k3ldar/PowerControlHub/KiCad/SmartFuseBox_PCB_Design_Specification.docx

# SmartFuseBox PCB Design Specification

# 1. Project Overview

The SmartFuseBox is a prototype PCB designed for both marine and home automation environments. It is based on the ESP32-S3 DevKitC-1 (N16R8) development board, which is mounted using headers to allow easy replacement. The board distributes 12V power through 8 relay channels (up to 5A each), includes at least 6 sensor input ports, a CAN bus interface, and monitoring features such as an onboard temperature sensor, buzzer, and fan connector. The system is designed for robust operation in demanding environments.

# 2. KiCad Project Structure

The KiCad project is structured as follows:

SmartFuseBox-PCB/
├── SmartFuseBox.kicad_pro
├── SmartFuseBox.kicad_sch ← root sheet (hierarchy only)
├── sheets/
│ ├── Power.kicad_sch
│ ├── ESP32_Module.kicad_sch
│ ├── Relays.kicad_sch
│ ├── Sensors.kicad_sch
│ └── Comms_Monitoring.kicad_sch
├── SmartFuseBox.kicad_pcb
└── gerbers/

# 3. ESP32-S3 DevKitC-1 Integration

The ESP32-S3 DevKitC-1 is mounted via dual-row headers. Essential pins for relays, sensors, CAN, buzzer, and fan are routed appropriately. USB access is maintained for programming. The ESP32 requires 3.3V power and robust grounding with short return paths.

# 4. Power System

The board accepts 12V DC input (up to 40A), distributed across 8 relays. DC-DC converters step down to 5V and 3.3V. Input filtering, reverse polarity protection, and fusing are required. Power planes are used for 12V, 5V, and 3.3V.

# 5. Relay Output System

8 relays with 12V coils (5A each) are driven by MOSFETs or transistors. Flyback diodes suppress voltage spikes. Relay outputs are connected to screw terminals. High-current traces use thick copper and are isolated from logic.

# 6. Sensor & IO Ports

At least 6 sensor ports provide 5V, 3.3V, GND, and two signal pins. All inputs include ESD protection and filtering. Screw terminals are recommended. Ports using GPIO35/36 support analog sensors. GPIO47/48 are digital-only. I2C-capable pairs include GPIO8/9 and GPIO10/11.

# 7. Communication Interfaces

A CAN transceiver interfaces with GPIO38 (TX) and GPIO39 (RX). Proper grounding and shielding are required. Termination resistors should be included as needed.

# 8. Monitoring & Auxiliary Features

Includes onboard temperature sensor (GPIO3), buzzer (GPIO1), and fan control (GPIO2). Optional status LEDs may be added.

# 9. Connector Strategy

Screw terminals are used for all power and sensor connections. ESP32 is socketed via headers. Dedicated connectors are provided for CAN, fan, and buzzer.

# 10. 4-Layer PCB Stackup Specification

Layer 1 — Top Layer: Signal + Low-Current Routing
Layer 2 — Inner Layer 1: Solid Ground Plane
Layer 3 — Inner Layer 2: Power Plane (12V, 5V, 3.3V)
Layer 4 — Bottom Layer: High-Current Relay Routing

# 11. Recommended Terminal Blocks

Use 5.0 mm pitch screw terminal blocks (≥10A rated) for power and relay outputs. Recommended series include:
- Phoenix Contact MKDS 5.08
- Wurth WR-TB series
- KF350-5.0 (generic)
Sensor ports may use 3.5 mm pitch blocks. All terminals should support AWG 12–24 wire sizes.

# Sheets

## Sheet 1 – Power Management

Circuit

Ref | Part | Value | KiCad Symbol | KiCad Footprint
J1 | Screw terminal 2-pin | 12V IN | Connector_PinHeader_2.54mm:PinHeader_1x02 | TerminalBlock_Phoenix:TerminalBlock_Phoenix_MPT-2.54mm_2P
F1 | Mini blade fuse holder | 20A | Device:Fuse | Fuse:Fuse_BelFuse_0AFF
Q1 | IRF9540N | P-ch MOSFET | Device:Q_PMOS_GSD | Package_TO_SOT_THT:TO-220-3_Vertical
TVS1 | P6KE15A | TVS 15V | Device:D_TVS | Diode_THT:D_DO-204AC
C1 | Electrolytic | 470µF/25V | Device:C | Capacitor_THT:CP_Radial_D10.0mm_P5.00mm
U1 | LM2596T-5.0 | Buck regulator | Regulator_Switching:LM2596T-5 | Package_TO_SOT_THT:TO-263-5_Vertical
L1 | Power inductor | 100µH/3A | Device:L | Inductor_THT:L_Radial_D8.0mm_P5.00mm
D1 | 1N5822 | Schottky 3A | Device:D_Schottky | Diode_THT:D_DO-201AD
C2 | Electrolytic | 100µF/10V | Device:C | Capacitor_THT:CP_Radial_D6.3mm_P2.50mm
U2 | AMS1117-3.3 | LDO 3.3V | Regulator_Linear:AMS1117-3.3 | Package_TO_SOT_SMD:SOT-223-3_TabPin2
C4/C5 | Tantalum | 10µF/10V | Device:C | Capacitor_SMD:C_0805_2012Metric

## Sheet 2 – ESP32-S3 Module

Houses the ESP32-S3 DevKitC-1 (N16R8) via two 20-pin female headers. All GPIO signals fan out as named nets to other sheets.

Please see 12. ESP32-S3 Pin Mapping

## Sheet 3 – Relay Drivers and Outputs

8-channel relay control using the ULN2803A Darlington array. Each relay has a status LED and a 3-pin screw terminal output (COM, NO, NC).

Ref | Part | Value | KiCad Symbol | KiCad Footprint
U3 | ULN2803ADWR | 8-ch Darlington | Driver_FET:ULN2803A | Package_SO:SOIC-18W_7.5x11.6mm_P1.27mm
RL1–RL8 | HRS4H-S-DC12V | 12V coil 10A SPDT | Relay_Electromechanical:G5LE-1 | Relay_THT:Relay_SPDT_HRS4H
J_RL1–8 | Screw terminal 3-pin | Relay output | Connector:Screw_Terminal_01x03 | TerminalBlock_Phoenix:TerminalBlock_Phoenix_MPT-2.54mm_3P
R_NET1 | Resistor network | 1kΩ×8 | Device:R_Network08 | Resistor_SMD:R_Array_Convex_8x0402
LED1–8 | LED 3mm green | — | Device:LED | LED_THT:LED_D3.0mm
R_LED1–8 | Resistor | 470Ω 0402 | Device:R | Resistor_SMD:R_0402
C_RL | Electrolytic | 100µF/25V | Device:C | Capacitor_THT:CP_Radial_D8.0mm_P5.00mm

## Sheet 4 - Sensor Ports and Switch Inputs

Six 5-pin sensor connectors (5V, 3.3V, GND, SIG1, SIG2) and four 2-pin switch/water-sensor inputs.

SENSOR_PORT_n (5-pin screw terminal):

Pin 1: +5V (from power rail, 100mA polyfuse per port: PTC_n)

Pin 2: +3.3V (from power rail, 100mA polyfuse per port)

Pin 3: GND

Pin 4: SIG1 → R_PU (10kΩ pullup to 3.3V) → ESP32 GPIO

Pin 5: SIG2 → R_PU (10kΩ pullup to 3.3V) → ESP32 GPIO

ESD protection:

D_ESD: PRTR5V0U2X or similar dual-channel TVS on SIG1/SIG2

# 12. ESP32-S3 Pin Mapping

## Relay Control Outputs

Relay Channel | ESP32 GPIO | Capabilities | Notes
Relay 1 | GPIO4 | Digital
Relay 2 | GPIO5 | Digital
Relay 3 | GPIO6 | Digital
Relay 4 | GPIO7 | Digital
Relay 5 | GPIO15 | Digital
Relay 6 | GPIO16 | Digital
Relay 7 | GPIO17 | Digital
Relay 8 | GPIO18 | Digital

## Sensor Input Ports

Sensor Port | Signal A | Signal B | Capabilities | Notes
Sensor 1 | GPIO8 | GPIO9 | Digital / I2C | I2C SDA/SCL capable
Sensor 2 | GPIO10 | GPIO11 | Digital / I2C | I2C SDA/SCL capable
Sensor 3 | GPIO12 | GPIO13 | Digital
Sensor 4 | GPIO14 | GPIO21 | Digital
Sensor 5 | GPIO47 | GPIO48 | Digital only | No ADC support
Sensor 6 | GPIO35 | GPIO36 | Analog only | ADC input only

## CAN Bus Interface

Function | ESP32 GPIO | Capabilities | Notes
CAN TX | GPIO38 | Digital
CAN RX | GPIO39 | Digital

## UART Interface

Function | ESP32 GPIO | Capabilities | Notes
UART TX | GPIO43 | USB-CDC | Avoid if using native USB
UART RX | GPIO44 | USB-CDC | Avoid if using native USB

⚠ If USB-CDC is used, reassign UART to GPIO1/2 or GPIO17/18.

## Auxiliary Outputs

Function | ESP32 GPIO | Capabilities | Notes
Buzzer | GPIO1 | Digital | Can be used for UART TX if needed
Cooling Fan | GPIO2 | Digital | Can be used for UART RX if needed

## Board Monitoring

Function | ESP32 GPIO | Capabilities | Notes
Temperature Sensor | GPIO3 | Analog | ADC input

## Reserved / Spare GPIO

GPIO | Capabilities | Notes
GPIO40 | Digital
GPIO41 | Digital
GPIO42 | Digital
GPIO45 | Input only | Do not use for output
GPIO46 | Input only | Do not use for output

## Power Pins

Function | Connection
5V | 5V regulator output
3.3V | 3.3V regulator output
GND | Ground plane
