k3ldar/PowerControlHub/KiCad/SmartFuseBox_PCB_Design_Specification.odt

SmartFuseBox PCB Design Specification

# 1. Project Overview

The SmartFuseBox is a prototype PCB designed for both marine and home automation environments. It is based on the ESP32-S3 DevKitC-1 (N16R8) development board, which is mounted using headers to allow easy replacement. The board is responsible for distributing 12V power through 8 relay channels, each capable of handling up to 5A. It includes multiple sensor input ports (minimum of 6), a CAN bus interface for future expansion, and monitoring features such as an onboard temperature sensor, buzzer, and fan connector. The system is designed for robust operation in demanding environments, ensuring reliable power distribution and sensor integration.

# 2. KiCad Project Structure

The KiCad project is structured as follows:

SmartFuseBox-PCB/
├── SmartFuseBox.kicad_pro
├── SmartFuseBox.kicad_sch ← root sheet (hierarchy only)
├── sheets/
│ ├── Power.kicad_sch
│ ├── ESP32_Module.kicad_sch
│ ├── Relays.kicad_sch
│ ├── Sensors.kicad_sch
│ └── Comms_Monitoring.kicad_sch
├── SmartFuseBox.kicad_pcb
└── gerbers/

• Power.kicad_sch: Defines the power input, regulation, and distribution circuits.
• ESP32_Module.kicad_sch: Contains the ESP32-S3 DevKitC-1 module and its connections.
• Relays.kicad_sch: Details the relay driver circuits and output connections.
• Sensors.kicad_sch: Defines the sensor input ports and signal conditioning.
• Comms_Monitoring.kicad_sch: Contains the CAN transceiver, temperature sensor, buzzer, and fan control circuits.

# 3. ESP32-S3 DevKitC-1 Integration

The ESP32-S3 DevKitC-1 is mounted via dual-row headers to allow easy replacement. Essential pins for controlling relays, reading sensor inputs, and interfacing with the CAN bus, buzzer, and fan must be routed to the appropriate circuits. USB access should be maintained for programming and debugging. The ESP32 requires 3.3V power and proper decoupling. Grounding must be robust, with short return paths and minimal noise coupling from high-current circuits.

# 4. Power System

The board accepts a 12V DC input capable of supplying up to 40A, distributed across 8 relay outputs. DC-DC converters step down the voltage to 5V and 3.3V for logic and sensors. Input filtering, reverse polarity protection, and fusing are required. Power planes should be used for 12V, 5V, and 3.3V, with careful placement of regulators to minimize noise and voltage drops. Recommended regulators include buck converters with sufficient current capacity and thermal management.

# 5. Relay Output System

The board includes 8 relays with 12V coils, each capable of switching up to 5A. Flyback diodes must be placed across each relay coil to suppress voltage spikes. MOSFET or transistor drivers are used to interface the ESP32 with the relays. Relay outputs are connected to screw terminals for easy wiring. High-current traces should be wide and use thick copper (e.g., 2 oz) to handle the load. Logic and high-current paths must be isolated to prevent interference.

# 6. Sensor & IO Ports

The board provides at least 6 sensor ports, each offering 5V, 3.3V, GND, and two signal pins. Additional digital inputs are available for switches or water sensors. All sensor inputs should include ESD protection and filtering. Screw terminals are recommended for sensor connections, with clear labeling and spacing for ease of use.

# 7. Communication Interfaces

A CAN transceiver is included for communication with future expansion boards. The CAN interface should use a standard connector and include termination resistors as needed. ESP32 GPIOs must be mapped appropriately to the CAN transceiver. Proper grounding and shielding practices should be followed to ensure signal integrity.

# 8. Monitoring & Auxiliary Features

The board includes an onboard temperature sensor for thermal monitoring, a buzzer for audible alerts, and a fan connector for active cooling. Optional status LEDs may be added for visual feedback. These components should be placed to avoid interference with other circuits and to ensure effective operation.

# 9. Connector Strategy

Screw terminals are used for all power and sensor connections to simplify wiring. The ESP32 is connected via header pins to allow easy replacement. Dedicated connectors are provided for the CAN interface, fan, and buzzer. All connectors should be clearly labeled and positioned for accessibility.

# 10. 4-Layer PCB Stackup Specification

## Layer 1 — Top Layer (Signal + Low-Current Routing)

This layer handles ESP32 high-speed signals, sensor IO, CAN bus, and control lines to relay drivers. It includes local decoupling capacitors and sensitive analog traces. Keep-out zones are defined around high-current relay pads. Critical signals such as the ESP32 crystal, USB, and boot pins are routed with minimal length.

## Layer 2 — Inner Layer 1 (Solid Ground Plane)

A continuous ground plane provides a low-impedance return path for high-speed signals and shields logic from high-current layers. Stitching vias are placed around the board perimeter. All components including the CAN transceiver, ESP32, sensors, and relay drivers are grounded to this layer.

## Layer 3 — Inner Layer 2 (Power Plane)

This layer distributes 12V, 5V, and 3.3V power. Wide copper pours are used for high-current 12V paths. Thermal reliefs are applied to connector pads. Logic and relay power are separated to reduce noise. Decoupling capacitors connect to this layer through vias.

## Layer 4 — Bottom Layer (High-Current Relay Routing)

This layer routes high-current relay outputs and coil connections. Heavy copper pours are used for 12V switching. Screw terminal connections are routed here. Logic traces are physically separated from high-current paths. Fan and buzzer power lines are also routed on this layer.

# 11. Summary

The SmartFuseBox PCB is a robust, modular power distribution and sensor interface board based on the ESP32-S3 DevKitC-1. It supports 12V power switching, sensor integration, and communication via CAN bus. The 4-layer PCB design ensures reliable operation by separating signal, ground, power, and high-current paths. This specification provides a comprehensive guide for implementing the design in KiCad.

# ESP32-S3 Pin Allocation

# ESP32-S3 DevKRelay Control Outputs (8 Channels)

These GPIO pins drive the relay driver circuits (via MOSFET/transistor drivers):

Relay Channel | ESP32 GPIO
Relay 1 | GPIO4
Relay 2 | GPIO5
Relay 3 | GPIO6
Relay 4 | GPIO7
Relay 5 | GPIO15
Relay 6 | GPIO16
Relay 7 | GPIO17
Relay 8 | GPIO18

### Sensor Input Ports

Each sensor connector provides:

- 5V
- 3.3V
- GND
- Signal A
- Signal B

Recommended GPIO assignments:

Sensor Port | Signal A | Signal B
Sensor 1 | GPIO8 | GPIO9
Sensor 2 | GPIO10 | GPIO11
Sensor 3 | GPIO12 | GPIO13
Sensor 4 | GPIO14 | GPIO21
Sensor 5 | GPIO47 | GPIO48
Sensor 6 | GPIO35 | GPIO36

These pins support:

- Digital sensors
- Analog sensors
- I2C devices
- Simple switch inputs

### CAN Bus Interface

The CAN bus is implemented using an external CAN transceiver.

Function | ESP32 GPIO
CAN TX | GPIO38
CAN RX | GPIO39

### UART Interface (External Devices / Debug)

Function | ESP32 GPIO
UART TX | GPIO43
UART RX | GPIO44

### Auxiliary Outputs

Function | ESP32 GPIO
Buzzer | GPIO1
Cooling Fan Control | GPIO2

### Board Monitoring

Function | ESP32 GPIO
On-board Temperature Sensor | GPIO3 (Analog Input)

### Reserved / Spare GPIO

The following pins should remain available for future expansion and should be routed to 5.0mm pitch PCB screw terminal blocks:

- GPIO40
- GPIO41
- GPIO42
- GPIO45
- GPIO46

### Power Pins

The following ESP32 power pins must be connected appropriately:

Function | Connection
5V | 5V regulator output
3.3V | 3.3V regulator output
GND | Ground plane

# itC-1 N16R8 ESP32 S3 WROOM-1-N16R8
