k3ldar/PowerControlHub/NextionControlPanel/src/Markers/CardinalMarkers.png

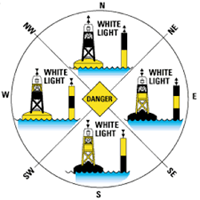
NextionControlPanel/src/Markers/CardinalMarkers.png
