k3ldar/PowerControlHub/NextionControlPanel/src/Markers/IsolatedDanger.png

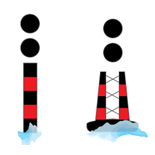
NextionControlPanel/src/Markers/IsolatedDanger.png
