k3ldar/PowerControlHub/NextionControlPanel/src/Markers/LateralPort.png

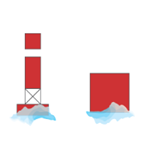
NextionControlPanel/src/Markers/LateralPort.png
