k3ldar/PowerControlHub/NextionControlPanel/src/Markers/PreferredChannelPort.png

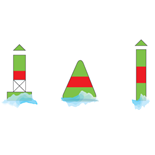
NextionControlPanel/src/Markers/PreferredChannelPort.png
