k3ldar/PowerControlHub/NextionControlPanel/src/Markers/SafeWater.png

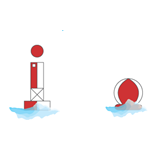
NextionControlPanel/src/Markers/SafeWater.png
