k3ldar/PowerControlHub/NextionControlPanel/src/Moon Phases/Phases.jpg

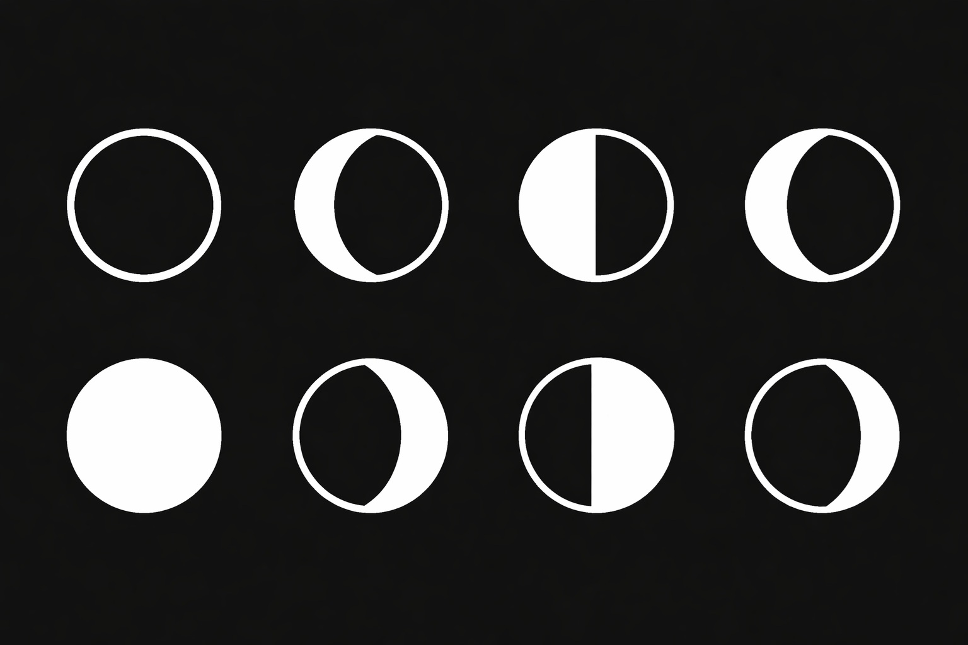
NextionControlPanel/src/Moon Phases/Phases.jpg
