k3ldar/PowerControlHub/PowerControlHub/SensorFactory.h

/*
 * PowerControlHub
 * Copyright (C) 2025 Simon Carter (s1cart3r@gmail.com)
 *
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
 * You should have received a copy of the GNU General Public License
 * along with this program. If not, see <https://www.gnu.org/licenses/>.
 */
#pragma once

#include "Local.h"
#include "Config.h"
#include "BaseSensor.h"
#include "MessageBus.h"
#include "SensorCommandHandler.h"
#include "WarningManager.h"
#include "RelayController.h"
#include "IWifiController.h"
#include "IBluetoothRadio.h"

#if defined(SD_CARD_SUPPORT)
#include "SdCardLogger.h"
#endif

#include "WaterSensorHandler.h"
#include "Dht11SensorHandler.h"
#include "GpsSensorHandler.h"
#include "LightSensorHandler.h"
#include "SystemSensorHandler.h"
#include "BinaryPresenceSensor.h"
#include "VoltageSensorHandler.h"
#include "ReedSensorHandler.h"

/**
 * @brief Dependencies injected by PowerControlHubApp into SensorFactory::create().
 *
 * Grouping them into a struct keeps the create() signature manageable and means
 * adding a new shared dependency does not require touching every call-site.
 */
struct SensorFactoryContext
{
    MessageBus* messageBus;
    BroadcastManager* broadcastManager;
    SensorCommandHandler* sensorCommandHandler;
    WarningManager* warningManager;
    RelayController* relayController;
    IWifiController* wifiController;
    IBluetoothRadio* bluetoothRadio;
    Stream* gpsSerial;

#if defined(SD_CARD_SUPPORT)
    SdCardLogger*         sdCardLogger;
#endif
};

/**
 * @brief Boot-time factory that converts SensorsConfig entries into live BaseSensor instances.
 *
 * Called once during setup(), after ConfigManager::load() has populated SensorsConfig.
 * All allocations are permanent for the lifetime of the device — no sensor is ever
 * destroyed or recreated at runtime.  A reboot is required for config changes to
 * take effect, which is intentional.
 *
 * Usage (inside PowerControlHubApp::setup):
 * @code
 *   SensorFactoryContext ctx{ &_messageBus, ... };
 *   uint8_t factoryCount = 0;
 *   BaseSensor** factorySensors = SensorFactory::create(config->sensors, ctx, factoryCount);
 * @endcode
 */
class SensorFactory
{
public:
    /**
     * @brief Allocate and initialise sensors described by @p sensorsConfig.
     *
     * Only entries with `enabled == true` are instantiated.  Entries whose
     * `sensorType` is not recognised are silently skipped — a warning is raised
     * if a WarningManager is available in @p ctx.
     *
     * @param sensorsConfig  Persistent config read from EEPROM.
     * @param ctx            Shared application-level dependencies.
     * @param[out] outCount  Number of sensors successfully created.
     * @return Heap-allocated array of BaseSensor* (may be nullptr if count == 0).
     */
    static BaseSensor** create(const SensorsConfig& sensorsConfig,
                               const SensorFactoryContext& ctx,
                               uint8_t& outCount)
    {
        outCount = 0;

        // First pass: count how many enabled config entries we can actually build,
        // excluding any SystemSensor entries (the system sensor is always added automatically)
        uint8_t capacity = 1; // +1 reserved for the automatic SystemSensor
        for (uint8_t i = 0; i < sensorsConfig.count && i < ConfigMaxSensors; i++)
        {
            if (sensorsConfig.sensors[i].enabled &&
                sensorsConfig.sensors[i].sensorType != SensorIdList::SystemSensor)
                capacity++;
        }

        BaseSensor** sensors = new BaseSensor*[capacity];

        for (uint8_t i = 0; i < sensorsConfig.count && i < ConfigMaxSensors; i++)
        {
            const SensorEntry& entry = sensorsConfig.sensors[i];

            if (!entry.enabled || entry.sensorType == SensorIdList::SystemSensor)
                continue;

            BaseSensor* sensor = createOne(entry, ctx);

            if (sensor != nullptr)
            {
                sensors[outCount++] = sensor;
            }
            else if (ctx.warningManager != nullptr)
            {
                ctx.warningManager->raiseWarning(WarningType::SensorFailure);
            }
        }

        // Always append the system sensor as the last entry
        sensors[outCount++] = createSystemSensor(ctx);

        return sensors;
    }

private:
    SensorFactory() = delete;

    static SystemSensorHandler* createSystemSensor(const SensorFactoryContext& ctx)
    {
        SystemSensorHandler* s = new SystemSensorHandler(
            ctx.messageBus,
            ctx.wifiController,
            ctx.bluetoothRadio,
            ctx.warningManager);

#if defined(SD_CARD_SUPPORT)
        if (ctx.sdCardLogger != nullptr)
            s->setSdCardLogger(ctx.sdCardLogger);
#endif

        return s;
    }

    static BaseSensor* createOne(const SensorEntry& entry, const SensorFactoryContext& ctx)
    {
        switch (entry.sensorType)
        {
            case SensorIdList::WaterSensor:
            {
                if (entry.pins[0] == PinDisabled || entry.pins[1] == PinDisabled)
                {
                    if (ctx.warningManager != nullptr)
                        ctx.warningManager->raiseWarning(WarningType::WaterSensorFailure);

                    return nullptr;
                }

                // pins[0] = sensor pin, pins[1] = active/power pin
                uint8_t sensorPin = entry.pins[0];
                uint8_t activePin = entry.pins[1];

                return new WaterSensorHandler(
                    ctx.broadcastManager,
                    ctx.sensorCommandHandler,
                    sensorPin,
                    activePin,
                    entry.name);
            }

            case SensorIdList::Dht11Sensor:
            {
                if (entry.pins[0] == PinDisabled)
                {
                    if (ctx.warningManager != nullptr)
                        ctx.warningManager->raiseWarning(WarningType::TemperatureSensorFailure);

                    return nullptr;
                }

                // pins[0] = data pin
                uint8_t sensorPin = entry.pins[0];
				float humidityOffset = static_cast<float>(entry.options2[0]) / 10.0f; // e.g. -5..+5% in steps of 0.1
                float temperatureOffset = static_cast<float>(entry.options2[1]) / 10.0f;

                return new Dht11SensorHandler(
                    ctx.broadcastManager,
                    ctx.sensorCommandHandler,
                    ctx.warningManager,
                    sensorPin,
                    humidityOffset,
                    temperatureOffset,
                    entry.name);
            }

            case SensorIdList::LightSensor:
            {
                if (entry.pins[0] == PinDisabled)
                {
                    if (ctx.warningManager != nullptr)
                        ctx.warningManager->raiseWarning(WarningType::LightSensorFailure);

                    return nullptr;
                }

                // pins[0] = sensor pin, options1[0] != 0 means digital mode
                uint8_t sensorPin = entry.pins[0];
                bool isDigital = (entry.options1[0] != 0);

                return new LightSensorHandler(
                    ctx.messageBus,
                    ctx.broadcastManager,
                    ctx.sensorCommandHandler,
                    ctx.relayController,
                    sensorPin,
                    isDigital,
                    entry.name);
            }

			case SensorIdList::BinaryPresenceSensor:
			{
                if (entry.pins[0] == PinDisabled)
                {
                    if (ctx.warningManager != nullptr)
                        ctx.warningManager->raiseWarning(WarningType::BinarySensorFailure);

                    return nullptr;
                }

                // pins[0] = sensor pin
				// options1[0] = active state (non-zero = HIGH, 0 = LOW)
				// options1[1] = onDetected action (ExecutionActionType)
				// pins[1] = onDetected action payload byte 0 (e.g. relay index)
				// options2[0] = onClear action (ExecutionActionType)
				// pins[2] = onClear action payload byte 0 (e.g. relay index)
				// options2[1] = pulse duration in seconds (shared; used when either action is RelayPulse)
				uint8_t sensorPin = entry.pins[0];
				int activeState = (entry.options1[0] != 0) ? HIGH : LOW;
				ExecutionActionType onDetectedAction = static_cast<ExecutionActionType>(entry.options1[1]);
				uint8_t onDetectedPayload = entry.pins[1];
				ExecutionActionType onClearAction = static_cast<ExecutionActionType>(static_cast<uint8_t>(entry.options2[0]));
				uint8_t onClearPayload = entry.pins[2];
				uint16_t pulseDurationSec = static_cast<uint16_t>(entry.options2[1]);
				return new BinaryPresenceSensor(
					ctx.messageBus,
					ctx.broadcastManager,
					ctx.sensorCommandHandler,
					ctx.relayController,
					sensorPin,
					activeState,
					entry.name,
					onDetectedAction,
					onDetectedPayload,
					onClearAction,
					onClearPayload,
					pulseDurationSec);
			}

            case SensorIdList::ReedSensor:
            {
                if (entry.pins[0] == PinDisabled)
                {
                    if (ctx.warningManager != nullptr)
                        ctx.warningManager->raiseWarning(WarningType::BinarySensorFailure);

                    return nullptr;
                }

                // pins[0] = sensor pin
                // pins[1] = active output pin (PinDisabled = not fitted)
                // options1[0] = contact type (0 = normally open, 1 = normally closed)
                uint8_t sensorPin = entry.pins[0];
                bool normallyOpen = (entry.options1[0] == ReedContactNormallyOpen);
                uint8_t activePin = entry.pins[1];

                return new ReedSensorHandler(
                    ctx.messageBus,
                    ctx.broadcastManager,
                    sensorPin,
                    normallyOpen,
                    activePin,
                    entry.name);
            }

            case SensorIdList::GpsSensor:
            {
#if defined(ESP32)
                // pins[0] = RX pin, pins[1] = TX pin, options1[0] = UART number (1 or 2; 0/unset defaults to 2)
                const uint8_t rxPin = entry.pins[0];
                const uint8_t txPin = entry.pins[1];

                if (rxPin == PinDisabled || txPin == PinDisabled)
                {
                    if (ctx.warningManager != nullptr)
                        ctx.warningManager->raiseWarning(WarningType::GpsInvalidConfig);

                    return nullptr;
                }

                const uint8_t uartNum = (entry.options1[0] == 1 || entry.options1[0] == 2)
                    ? static_cast<uint8_t>(entry.options1[0])
                    : 2;

                // HardwareSerial is allocated once; ownership transferred to GpsSensorHandler via Stream*.
                HardwareSerial* hwSerial = new HardwareSerial(uartNum);
                hwSerial->begin(GpsBaudRate, SERIAL_8N1, rxPin, txPin);

                return new GpsSensorHandler(
                    hwSerial,
                    ctx.broadcastManager,
                    ctx.sensorCommandHandler,
                    ctx.warningManager,
                    entry.name);
#else
                if (ctx.gpsSerial == nullptr)
                {
                    if (ctx.warningManager != nullptr)
                        ctx.warningManager->raiseWarning(WarningType::GpsInvalidConfig);
                    return nullptr;
                }

                return new GpsSensorHandler(
                    ctx.gpsSerial,
                    ctx.broadcastManager,
                    ctx.sensorCommandHandler,
                    ctx.warningManager,
                    entry.name);
#endif
            }

            case SensorIdList::VoltageSensor:
            {
                if (entry.pins[0] == PinDisabled)
                {
                    if (ctx.warningManager != nullptr)
                        ctx.warningManager->raiseWarning(WarningType::VoltageSensorFailure);

                    return nullptr;
                }
                
                // pins[0] = analog sensor pin
                // options1[0] = ADC Vref in tenths of a volt (e.g. 50 = 5.0 V); 0 = default (5.0 V)
                // options1[1] = R2 in tenths of kΩ (e.g. 75 = 7.5 kΩ);          0 = default (7.5 kΩ)
                // options2[0] = R1 in whole kΩ (e.g. 30 = 30 kΩ);               0 = default (30 kΩ)
                // options2[1] = low-voltage warning threshold in tenths of a volt (e.g. 114 = 11.4 V); 0 = disabled
                return new VoltageSensorHandler(
                    ctx.broadcastManager,
                    ctx.warningManager,
                    entry.pins[0],
                    entry.options1[0],
                    entry.options2[0],
                    entry.options1[1],
                    entry.options2[1],
                    entry.name);
            }

            default:
                return nullptr;
        }
    }
};
