k3ldar/PowerControlHub/PowerControlHub/PowerControlHubApp.h

/*
 * PowerControlHub
 * Copyright (C) 2025 Simon Carter (s1cart3r@gmail.com)
 *
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
 * You should have received a copy of the GNU General Public License
 * along with this program. If not, see <https://www.gnu.org/licenses/>.
 */
#pragma once

#include "Local.h"

#include <memory>

#include <SerialCommandManager.h>
#include <SensorManager.h>

#include "PowerControlHubConstants.h"
#include "MessageBus.h"
#include "RelayController.h"
#include "SoundController.h"
#include "WarningManager.h"
#include "SystemFunctions.h"
#include "RelayCommandHandler.h"
#include "SoundCommandHandler.h"
#include "InterceptDebugCommandHandler.h"
#include "SensorCommandHandler.h"
#include "SensorConfigCommandHandler.h"
#include "WarningCommandHandler.h"
#include "AckCommandHandler.h"
#include "SystemCommandHandler.h"
#include "ConfigCommandHandler.h"
#include "NextionConfigCommandHandler.h"
#include "ExternalSensorConfigCommandHandler.h"
#include "ExternalSensorNetworkHandler.h"
#include "BluetoothRadioBridge.h"
#include "IBluetoothRadio.h"
#include "WifiController.h"
#include "IWifiController.h"
#include "ConfigController.h"
#include "SensorController.h"
#include "ConfigNetworkHandler.h"
#include "RelayNetworkHandler.h"
#include "SoundNetworkHandler.h"
#include "SystemNetworkHandler.h"
#include "SensorNetworkHandler.h"
#include "WarningNetworkHandler.h"
#include "SchedulerNetworkHandler.h"
#include "WebIndexNetworkHandler.h"
#include "WifiCommandBridge.h"

#if defined(SD_CARD_SUPPORT)
#include "SdCardLogger.h"
#include "MicroSdDriver.h"
#include "SDCardConfigLoader.h"
#endif

#if defined(MQTT_SUPPORT)
#include "MQTTController.h"
#include "MQTTConfigCommandHandler.h"
#include "MQTTRelayHandler.h"
#include "MQTTSensorHandler.h"
#include "MQTTSystemHandler.h"
#endif

#include "SchedulerCommandHandler.h"
#include "ScheduleController.h"

#if defined(LED_MANAGER)
#include "LedMatrixManager.h"
#endif

#if defined(OTA_AUTO_UPDATE) && defined(ESP32) && defined(WIFI_SUPPORT)
#include "OtaManager.h"
#endif

#if defined(NEXTION_DISPLAY_DEVICE)
#include <NextionControl.h>
#endif

#include "BaseSensor.h"
#include "RemoteSensor.h"
#include "SensorFactory.h"

class PowerControlHubApp
{
private:
    SerialCommandManager* _commandMgrComputer;

    MessageBus _messageBus;
    RelayController _relayController;
    SoundController _soundController;
    BroadcastManager _broadcastManager;
    WarningManager _warningManager;

#if defined(NEXTION_DISPLAY_DEVICE)
    NextionControl* _nextionControl;
#endif

    RelayCommandHandler _relayHandler;
    SoundCommandHandler _soundHandler;
    InterceptDebugHandler _interceptDebugHandler;
    SensorCommandHandler _sensorCommandHandler;
    SensorConfigCommandHandler _sensorConfigHandler;
    WarningCommandHandler _warningCommandHandler;
    AckCommandHandler _ackHandler;
    SystemCommandHandler _systemCommandHandler;


    PlatformBluetoothRadio _bluetoothController;
    WifiController _wifiController;

    ConfigController _configController;
    ConfigCommandHandler _configHandler;
    NextionConfigCommandHandler _nextionConfigHandler;
    ExternalSensorConfigCommandHandler _externalSensorConfigHandler;

    ConfigNetworkHandler _configNetworkHandler;
    RelayNetworkHandler _relayNetworkHandler;
    SoundNetworkHandler _soundNetworkHandler;
    WarningNetworkHandler _warningNetworkHandler;
    SystemNetworkHandler _systemNetworkHandler;
    SensorNetworkHandler* _sensorNetworkHandler;
	WebIndexNetworkHandler* _webIndexNetworkHandler;

#if defined(SD_CARD_SUPPORT)
    SdCardLogger _sdCardLogger;
#endif

    SensorManager* _sensorManager;
    SensorController* _sensorController;
    BaseSensor** _factorySensors;
    uint8_t _factorySensorCount;
    Stream* _gpsSerial;
    RemoteSensor** _remoteSensors;
    uint8_t _remoteSensorCount;

#if defined(MQTT_SUPPORT)
    MQTTController _mqttController;
    MQTTConfigCommandHandler _mqttConfigHandler;
    MQTTRelayHandler _mqttRelayHandler;
    MQTTSensorHandler* _mqttSensorHandler;
    MQTTSystemHandler _mqttSystemHandler;
    uint64_t _nextRunMqttMs;
#endif

	SchedulerCommandHandler _schedulerCommandHandler;
	SchedulerNetworkHandler _schedulerNetworkHandler;
	ExternalSensorNetworkHandler _externalSensorNetworkHandler;
	WifiCommandBridge _wifiCommandBridge;

	// Persistent storage for the serial handler array so WifiCommandBridge
	// can hold a pointer to it safely beyond setup().
	static constexpr uint8_t MaxSerialHandlerCount = 12;
	ISerialCommandHandler* _serialHandlers[MaxSerialHandlerCount];
	uint8_t _serialHandlerCount;
	ScheduleController _scheduleController;
	uint64_t _pendingRebootTime;

#if defined(LED_MANAGER)
    LedMatrixManager _ledManager;
#endif

#if defined(OTA_AUTO_UPDATE) && defined(ESP32) && defined(WIFI_SUPPORT)
    OtaManager _otaManager;
#endif

#if defined(CARD_CONFIG_LOADER)
    SdCardConfigLoader _sdCardConfigLoader;
    static PowerControlHubApp* _instance;
    static void onSdCardReadyCallback(bool isNewCard);
#endif

    void configureWifiSupport(Config* config);
    void configureBluetoothSupport(Config* config);

public:
    explicit PowerControlHubApp(SerialCommandManager* commandMgrComputer);

    void setup(RemoteSensor** remoteSensors, uint8_t remoteSensorCount);
    void loop();

    void setGpsSerial(Stream* gpsSerial) { _gpsSerial = gpsSerial; }

    MessageBus* messageBus() { return &_messageBus; }
    BroadcastManager* broadcastManager() { return &_broadcastManager; }
    WarningManager* warningManager() { return &_warningManager; }
    SensorCommandHandler* sensorCommandHandler() { return &_sensorCommandHandler; }
    RelayController* relayController() { return &_relayController; }

    IWifiController* wifiController() 
    {
        return &_wifiController;
    }

    IBluetoothRadio* bluetoothController()
    {
        return &_bluetoothController;
    }

#if defined(SD_CARD_SUPPORT)
    SdCardLogger* sdCardLogger()
    {
        return &_sdCardLogger;
    }
#endif
};
