k3ldar/PowerControlHub/PowerControlHub/MQTTSensorHandler.cpp

/*
 * PowerControlHub
 * Copyright (C) 2025 Simon Carter (s1cart3r@gmail.com)
 *
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
 * You should have received a copy of the GNU General Public License
 * along with this program. If not, see <https://www.gnu.org/licenses/>.
 */
#include "Local.h"

#if defined(MQTT_SUPPORT)
#include "MQTTSensorHandler.h"
#include "RemoteSensor.h"
#include "SystemDefinitions.h"
#include "SystemFunctions.h"
#include <SerialCommandManager.h>
#include <string.h>
#include <stdio.h>

const char PROGMEM JsonBase[] = "{\"name\":\"%s\",\"state_topic\":\"home/%s/sensor/%s/state\"";
const char PROGMEM JsonBinaryPayload[] = ",\"payload_on\":\"ON\",\"payload_off\":\"OFF\"";
const char PROGMEM JsonDeviceClass[] = ",\"device_class\":\"%s\"";
const char PROGMEM JsonUnit[] = ",\"unit_of_measurement\":\"%s\"";
const char PROGMEM JsonFooter[] = ",\"unique_id\":\"%s_%s\",\"device\":{\"ids\":[\"%s\"],\"name\":\"Smart Fuse Box\",\"mf\":\"Simon Carter\",\"mdl\":\"SFB v1\"}}";
const char PROGMEM DiscoveryTopicFormat[] = "%s/%s/%s/%s/config";
const char PROGMEM StateTopicFormat[] = "home/%s/sensor/%s/state";
const char PROGMEM SetTopicFormat[] = "home/%s/sensor/%s/set";
const char PROGMEM EntityTypeBinarySensor[] = "binary_sensor";
const char PROGMEM EntityTypeSensor[] = "sensor";

MQTTSensorHandler::MQTTSensorHandler(MQTTController* mqttController, MessageBus* messageBus, SensorController* sensorController, SerialCommandManager* commandMgr)
    : MQTTHandler(mqttController, messageBus),
        _config(nullptr),
        _sensorController(sensorController),
        _commandMgr(commandMgr),
        _discoveryPending(false),
        _discoveryIndex(0),
        _lastDiscoveryPublish(0)
{
    _config = ConfigManager::getConfigPtr();
}

bool MQTTSensorHandler::begin()
{
    if (_mqttController == nullptr || _messageBus == nullptr || _config == nullptr || _sensorController == nullptr)
    {
        if (_commandMgr != nullptr)
        {
            _commandMgr->sendError(F("Required components not available"), F("MQTT Sensor"));
        }
        return false;
    }

    _messageBus->subscribe<TemperatureUpdated>(
        [this](float temp)
        {
            this->onTemperatureUpdated(temp);
        }
    );

    _messageBus->subscribe<HumidityUpdated>(
        [this](uint8_t humidity)
        {
            this->onHumidityUpdated(humidity);
        }
    );

    _messageBus->subscribe<LightSensorUpdated>(
        [this](bool isDaytime, uint16_t lightLevel, uint16_t averageLightLevel)
        {
            this->onLightSensorUpdated(isDaytime, lightLevel, averageLightLevel);
        }
    );

    _messageBus->subscribe<WaterLevelUpdated>(
        [this](uint16_t waterLevel, uint16_t averageWaterLevel)
        {
            this->onWaterLevelUpdated(waterLevel, averageWaterLevel);
        }
    );

    // Build channel map from sensor controller
    _channelMap.clear();
    _typeSlugToIndices.clear();

    for (uint8_t s = 0; s < _sensorController->sensorCount(); s++)
    {
        BaseSensor* sensor = _sensorController->sensorGet(s);

        if (sensor == nullptr)
        {
            continue;
        }

        for (uint8_t c = 0; c < sensor->getMqttChannelCount(); c++)
        {
            // Get channel info and cache typeSlug (Option 4)
            MqttSensorChannel ch = sensor->getMqttChannel(c);
            uint8_t channelIndex = static_cast<uint8_t>(_channelMap.size());

            // Cache publish interval from sensor (Option 1)
            uint64_t interval = sensor->getMqttPublishIntervalMs(c);

            _channelMap.push_back({ sensor, c, ch.typeSlug, 0, interval });

            // Build typeSlug-to-indices map for fast event lookup (Option 1)
            if (ch.typeSlug != nullptr)
            {
                _typeSlugToIndices[ch.typeSlug].push_back(channelIndex);
            }
        }
    }

    _messageBus->subscribe<SystemMetricsUpdated>(
        [this]()
        {
            for (uint8_t i = 0; i < _channelMap.size(); i++)
            {
                this->publishSensorState(i);
            }
        }
    );

    _messageBus->subscribe<MqttConnected>(
        [this]()
        {
            this->subscribe();

            if (_config != nullptr && _config->mqtt.useHomeAssistantDiscovery)
            {
                _discoveryPending = true;
                _discoveryIndex = 0;
            }

            for (uint8_t i = 0; i < _channelMap.size(); i++)
            {
                this->publishSensorState(i);
            }
        }
    );

    _messageBus->subscribe<MqttMessageReceived>(
        [this](const char* topic, const char* payload)
        {
            this->onMessage(topic, payload);
        }
    );

    return true;
}

void MQTTSensorHandler::update()
{
    uint64_t now = SystemFunctions::millis64();

    if (_discoveryPending && _discoveryIndex < _channelMap.size())
    {
        if (_mqttController != nullptr && _mqttController->isConnected())
        {
            if (now - _lastDiscoveryPublish >= MinPublishInterval)
            {
                publishSensorDiscoveryConfig(_discoveryIndex);
                _lastDiscoveryPublish = now;
                _discoveryIndex++;

                if (_discoveryIndex >= _channelMap.size())
                {
                    if (_commandMgr != nullptr)
                    {
                        _commandMgr->sendDebug(F("Sensor discovery complete"), F("MQTT"));
                    }
                    _discoveryPending = false;
                }
            }
        }
    }
}

void MQTTSensorHandler::end()
{
    unsubscribe();
    _isSubscribed = false;
}

void MQTTSensorHandler::onMessage(const char* topic, const char* payload)
{
    if (topic == nullptr || payload == nullptr)
        return;

    if (_config == nullptr || _sensorController == nullptr)
        return;

    char expectedTopic[MqttMaxTopicLength];
    for (uint8_t s = 0; s < _sensorController->sensorCount(); s++)
    {
        BaseSensor* sensor = _sensorController->sensorGet(s);
        if (sensor == nullptr || sensor->getSensorType() != SensorType::Remote)
            continue;

        snprintf_P(expectedTopic, sizeof(expectedTopic), SetTopicFormat, _config->mqtt.deviceId, sensor->getSafeSlug());

        if (strcmp(topic, expectedTopic) != 0)
            continue;

        // Parse "lat=X;lon=Y" payload — order-independent
        double lat = 0.0, lon = 0.0;
        bool hasLat = false, hasLon = false;
        const char* p = payload;

        while (*p)
        {
            if (strncmp(p, "lat=", 4) == 0) { lat = atof(p + 4); hasLat = true; }
            else if (strncmp(p, "lon=", 4) == 0) { lon = atof(p + 4); hasLon = true; }
            while (*p && *p != ';') p++;
            if (*p == ';') p++;
        }

        if (!hasLat || !hasLon)
        {
            return;
        }

        // Build params matching GPS channel order: [0]=lat, [1]=lon
        StringKeyValue params[2];
        strncpy(params[0].key, "lat", sizeof(params[0].key) - 1);
        params[0].key[sizeof(params[0].key) - 1] = '\0';
        dtostrf(lat, 1, 6, params[0].value);

        strncpy(params[1].key, "lon", sizeof(params[1].key) - 1);
        params[1].key[sizeof(params[1].key) - 1] = '\0';
        dtostrf(lon, 1, 6, params[1].value);

        static_cast<RemoteSensor*>(sensor)->handleRemoteCommand(params, 2);

        if (sensor->getSensorIdType() == SensorIdList::GpsSensor && _messageBus != nullptr)
        {
            _messageBus->publish<GpsLocationUpdated>(lat, lon);
        }

        // Republish updated state channels so HA reflects the new values
        uint64_t now = SystemFunctions::millis64();
        for (uint8_t i = 0; i < _channelMap.size(); i++)
        {
            if (_channelMap[i].sensor == sensor)
            {
                publishSensorState(i);
                _channelMap[i].lastPublishTime = now;
            }
        }

        return;
    }
}

bool MQTTSensorHandler::subscribe()
{
    if (_mqttController == nullptr || _config == nullptr || _sensorController == nullptr)
        return false;

    MQTTClient* client = _mqttController->getClient();
    if (client == nullptr || !client->isConnected())
        return false;

    bool result = true;
    char topic[MqttMaxTopicLength];

    for (uint8_t s = 0; s < _sensorController->sensorCount(); s++)
    {
        BaseSensor* sensor = _sensorController->sensorGet(s);
        if (sensor == nullptr || sensor->getSensorType() != SensorType::Remote)
            continue;

        snprintf_P(topic, sizeof(topic), SetTopicFormat, _config->mqtt.deviceId, sensor->getSafeSlug());

        if (!client->subscribe(topic, MqttQoS::AtMostOnce))
            result = false;

        if (_commandMgr != nullptr)
            _commandMgr->sendDebug(topic, F("MQTT Sensor Subscribe"));
    }

    _isSubscribed = result;
    return result;
}

void MQTTSensorHandler::unsubscribe()
{
    if (_mqttController != nullptr && _config != nullptr && _sensorController != nullptr)
    {
        MQTTClient* client = _mqttController->getClient();
        if (client != nullptr)
        {
            char topic[MqttMaxTopicLength];
            for (uint8_t s = 0; s < _sensorController->sensorCount(); s++)
            {
                BaseSensor* sensor = _sensorController->sensorGet(s);
                if (sensor == nullptr || sensor->getSensorType() != SensorType::Remote)
                    continue;

                snprintf_P(topic, sizeof(topic), SetTopicFormat, _config->mqtt.deviceId, sensor->getSafeSlug());
                client->unsubscribe(topic);
            }
        }
    }

    _isSubscribed = false;
}

// ============================================================================
// Private Methods
// ============================================================================

void MQTTSensorHandler::onTemperatureUpdated(float temperature)
{
    (void)temperature;

    uint64_t now = SystemFunctions::millis64();
    auto it = _typeSlugToIndices.find("temperature");
    if (it != _typeSlugToIndices.end())
    {
        for (uint8_t i = 0; i < it->second.size(); i++)
        {
            uint8_t idx = it->second[i];
            MqttChannelMap& channel = _channelMap[idx];

            if (now - channel.lastPublishTime >= channel.publishIntervalMs)
            {
                publishSensorState(idx);
                channel.lastPublishTime = now;
            }
        }
    }
}

void MQTTSensorHandler::onHumidityUpdated(uint8_t humidity)
{
    (void)humidity;

    uint64_t now = SystemFunctions::millis64();
    auto it = _typeSlugToIndices.find("humidity");
    if (it != _typeSlugToIndices.end())
    {
        for (uint8_t i = 0; i < it->second.size(); i++)
        {
            uint8_t idx = it->second[i];
            MqttChannelMap& channel = _channelMap[idx];

            if (now - channel.lastPublishTime >= channel.publishIntervalMs)
            {
                publishSensorState(idx);
                channel.lastPublishTime = now;
            }
        }
    }
}

void MQTTSensorHandler::onLightSensorUpdated(bool isDaytime, uint16_t lightLevel, uint16_t averageLightLevel)
{
    (void)isDaytime;
    (void)lightLevel;
    (void)averageLightLevel;

    uint64_t now = SystemFunctions::millis64();

    // Publish all light-related channels
    const char* lightTypes[] = { "light", "light_level", "avg_light_level" };
    for (uint8_t t = 0; t < 3; t++)
    {
        auto it = _typeSlugToIndices.find(lightTypes[t]);
        if (it != _typeSlugToIndices.end())
        {
            for (uint8_t i = 0; i < it->second.size(); i++)
            {
                uint8_t idx = it->second[i];
                MqttChannelMap& channel = _channelMap[idx];

                if (now - channel.lastPublishTime >= channel.publishIntervalMs)
                {
                    publishSensorState(idx);
                    channel.lastPublishTime = now;
                }
            }
        }
    }
}

void MQTTSensorHandler::onWaterLevelUpdated(uint16_t waterLevel, uint16_t averageWaterLevel)
{
    (void)waterLevel;
    (void)averageWaterLevel;

    uint64_t now = SystemFunctions::millis64();
    auto it = _typeSlugToIndices.find("water_level");
    if (it != _typeSlugToIndices.end())
    {
        for (uint8_t i = 0; i < it->second.size(); i++)
        {
            uint8_t idx = it->second[i];
            MqttChannelMap& channel = _channelMap[idx];

            if (now - channel.lastPublishTime >= channel.publishIntervalMs)
            {
                publishSensorState(idx);
                channel.lastPublishTime = now;
            }
        }
    }
}

void MQTTSensorHandler::publishSensorState(uint8_t channelIndex)
{
    if (_mqttController == nullptr || _config == nullptr)
    {
        return;
    }

    if (!_mqttController->isConnected())
    {
        return;
    }

    if (channelIndex >= _channelMap.size())
    {
        return;
    }

    const MqttChannelMap& entry = _channelMap[channelIndex];
    MqttSensorChannel channel = entry.sensor->getMqttChannel(entry.channelIndex);

    char topic[MqttMaxTopicLength];
    char payload[32];

    snprintf_P(topic, sizeof(topic), StateTopicFormat, _config->mqtt.deviceId, channel.slug);
    entry.sensor->getMqttValue(entry.channelIndex, payload, sizeof(payload));

    _mqttController->publishState(topic, payload);
}

void MQTTSensorHandler::publishDiscoveryConfig()
{
    _discoveryPending = true;
    _discoveryIndex = 0;
}

void MQTTSensorHandler::publishSensorDiscoveryConfig(uint8_t index)
{
    if (_mqttController == nullptr || _config == nullptr)
    {
        return;
    }

    if (!_mqttController->isConnected())
    {
        return;
    }

    if (index >= _channelMap.size())
    {
        return;
    }

    MQTTClient* client = _mqttController->getClient();

    if (client == nullptr)
    {
        return;
    }

    const MqttChannelMap& entry = _channelMap[index];
    MqttSensorChannel channel = entry.sensor->getMqttChannel(entry.channelIndex);

    char topic[MqttMaxTopicLength];
    char payload[MqttMaxPayloadLength];

    const char* entityType = channel.isBinary ? EntityTypeBinarySensor : EntityTypeSensor;

    int topicLen = snprintf_P(topic, sizeof(topic), DiscoveryTopicFormat,
        _config->mqtt.discoveryPrefix, entityType, _config->mqtt.deviceId, channel.slug);
    if (topicLen < 0 || topicLen >= static_cast<int>(sizeof(topic)))
    {
        if (_commandMgr != nullptr)
        {
            _commandMgr->sendError(F("Discovery topic truncated"), F("MQTT Sensor"));
        }
        return;
    }

    // payload[512]
    size_t offset = 0;
    size_t remaining = sizeof(payload);

    int ret = snprintf_P(payload, remaining, JsonBase,
        channel.name,
        _config->mqtt.deviceId, channel.slug);

    if (ret > 0 && static_cast<size_t>(ret) < remaining)
    {
        offset += static_cast<size_t>(ret);
        remaining -= static_cast<size_t>(ret);
    }
    else
    {
        remaining = 0;
    }

    if (channel.isBinary && remaining > 0)
    {
        ret = snprintf_P(payload + offset, remaining, JsonBinaryPayload);

        if (ret > 0 && static_cast<size_t>(ret) < remaining)
        {
            offset += static_cast<size_t>(ret);
            remaining -= static_cast<size_t>(ret);
        }
        else
        {
            remaining = 0;
        }
    }

    if (channel.deviceClass != nullptr && remaining > 0)
    {
        ret = snprintf_P(payload + offset, remaining, JsonDeviceClass,
            channel.deviceClass);

        if (ret > 0 && static_cast<size_t>(ret) < remaining)
        {
            offset += static_cast<size_t>(ret);
            remaining -= static_cast<size_t>(ret);
        }
        else
        {
            remaining = 0;
        }
    }

    if (channel.unit != nullptr && remaining > 0)
    {
        ret = snprintf_P(payload + offset, remaining, JsonUnit,
            channel.unit);

        if (ret > 0 && static_cast<size_t>(ret) < remaining)
        {
            offset += static_cast<size_t>(ret);
            remaining -= static_cast<size_t>(ret);
        }
        else
        {
            remaining = 0;
        }
    }

    if (remaining > 0)
    {
        snprintf_P(payload + offset, remaining, JsonFooter,
            _config->mqtt.deviceId, channel.slug,
            _config->mqtt.deviceId);
    }

    client->publish(topic, payload, MqttQoS::AtMostOnce, true);
}
#endif
