k3ldar/PowerControlHub/PowerControlHub/RelayController.h

/*
 * PowerControlHub
 * Copyright (C) 2025 Simon Carter (s1cart3r@gmail.com)
 *
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
 * You should have received a copy of the GNU General Public License
 * along with this program. If not, see <https://www.gnu.org/licenses/>.
 */
#pragma once

#include "SystemDefinitions.h"
#include "ConfigManager.h"
#include "MessageBus.h"
#include "SoundController.h"

enum class RelayResult : uint8_t
{
	Success = 0,
	InvalidIndex = 1,
	Reserved = 2,
	InvalidConfig = 3,
	InvalidParameter = 4,
	Failed = 5
};


class RelayController
{
private:
	MessageBus* _messageBus;
	SoundController* _soundController;
	bool* _relayStatus;
	uint8_t* _relays;
	uint8_t _relayCount;

	bool isHornRelay(uint8_t relayIndex) const
	{
		Config* config = ConfigManager::getConfigPtr();
		if (config == nullptr || relayIndex >= _relayCount)
			return false;
		return config->relay.relays[relayIndex].actionType == RelayActionType::Horn;
	}

	bool isRelayDisabled(uint8_t relayIndex) const
	{
		return _relays[relayIndex] == PinDisabled;
	}

	RelayResult setRelayStatus(uint8_t relayIndex, bool isOn)
	{
		if (relayIndex >= _relayCount)
		{
			return RelayResult::InvalidIndex;
		}

		if (isHornRelay(relayIndex))
		{
			return RelayResult::Reserved;
		}

		// Compute which relays actually change state so subscribers can be notified
		uint8_t changedMask = 0;

		// Primary relay — only write hardware if the pin is assigned
		if (_relayStatus[relayIndex] != isOn)
		{
			_relayStatus[relayIndex] = isOn;
			if (!isRelayDisabled(relayIndex))
			{
				digitalWrite(_relays[relayIndex], isOn ? LOW : HIGH);
			}
			changedMask |= (1 << relayIndex);
		}

		Config* config = ConfigManager::getConfigPtr();

		if (config != nullptr)
		{
			// Check for linked relays and update only if their state changes
				for (uint8_t i = 0; i < ConfigMaxLinkedRelays; i++)
				{
					if (config->relay.linkedRelays[i][0] == relayIndex)
					{
						uint8_t linkedRelay = config->relay.linkedRelays[i][1];
						if (linkedRelay < _relayCount && !isRelayDisabled(linkedRelay))
						{
							if (_relayStatus[linkedRelay] != isOn)
							{
								_relayStatus[linkedRelay] = isOn;
								digitalWrite(_relays[linkedRelay], isOn ? LOW : HIGH);
								changedMask |= (1 << linkedRelay);
							}
						}
					}
				}
		}

		if (_messageBus && changedMask)
		{
			// Publish bitmask of relays that actually changed state
			_messageBus->publish<RelayStatusChanged>(changedMask);
		}

		return RelayResult::Success;
	}

public:
	RelayController(MessageBus* messageBus, const uint8_t* relayPins, uint8_t totalRelays)
		: _messageBus(messageBus), _soundController(nullptr), _relayStatus(nullptr), _relays(nullptr), _relayCount(totalRelays)
	{
		_relays = new uint8_t[_relayCount];
		memcpy(_relays, relayPins, sizeof(uint8_t)* _relayCount);

		_relayStatus = new bool[_relayCount];

		for (uint8_t i = 0; i < totalRelays; i++)
		{
			_relayStatus[i] = false;
		}
	}

	~RelayController()
	{
		delete[] _relayStatus;
		delete[] _relays;
	}

	void setup()
	{
		for (uint8_t i = 0; i < _relayCount; i++)
		{
			_relayStatus[i] = false;
			if (!isRelayDisabled(i))
			{
				pinMode(_relays[i], OUTPUT);
				digitalWrite(_relays[i], HIGH);
			}
		}
	}

	CommandResult turnAllRelaysOff()
	{
		for (int i = 0; i < _relayCount; i++)
		{
			setRelayStatus(i, false);
		}
		
		return CommandResult::ok();
	}

	CommandResult turnAllRelaysOn()
	{
		for (int i = 0; i < _relayCount; i++)
		{
			setRelayStatus(i, true);
		}
		return CommandResult::ok();
	}

	CommandResult setRelayState(uint8_t relayIndex, bool state)
	{
		RelayResult result = setRelayStatus(relayIndex, state);

		if (result == RelayResult::Success)
		{
			// Return actual state for confirmation
			return CommandResult::okStatus(static_cast<uint8_t>(_relayStatus[relayIndex] ? 1 : 0));
		}

		return CommandResult::error(static_cast<uint8_t>(result));
	}

	CommandResult getRelayStatus(uint8_t relayIndex)
	{
		uint8_t status = PinDisabled;

		if (relayIndex < _relayCount)
		{
			status = _relayStatus[relayIndex] ? 1 : 0;
		}

		return CommandResult::okStatus(status);
	}

	CommandResult getAllRelayStates() const
	{
		uint8_t bitmask = 0;
		for (uint8_t i = 0; i < _relayCount && i < 8; i++)
		{
			if (_relayStatus[i])
			{
				bitmask |= (1 << i);
			}
		}

		return CommandResult::okStatus(bitmask);
	}

	uint8_t getRelayCount() const { return _relayCount; }

	bool isDisabled(uint8_t relayIndex) const
	{
		if (relayIndex >= _relayCount)
			return true;

		return isRelayDisabled(relayIndex);
	}

	// Refresh the pin array from persisted config (call after ConfigManager::load()).
	// Disabled relays (pin == PinDisabled) will be skipped by all hardware writes.
	void syncPinsFromConfig()
	{
		Config* config = ConfigManager::getConfigPtr();

		if (config == nullptr)
			return;

		for (uint8_t i = 0; i < _relayCount; i++)
		{
			_relays[i] = config->relay.relays[i].pin;
		}
	}

	void setSoundController(SoundController* soundController)
	{
		_soundController = soundController;
	}

	RelayResult setRelayActionType(uint8_t relayIndex, RelayActionType actionType)
	{
		Config* config = ConfigManager::getConfigPtr();
		if (config == nullptr)
			return RelayResult::InvalidConfig;

		if (relayIndex >= _relayCount)
			return RelayResult::InvalidIndex;

		if (actionType > RelayActionType::NightRelay)
			return RelayResult::InvalidParameter;

		// Enforce single-instance: clear other relays that hold the same type
		if (actionType != RelayActionType::Default)
		{
			for (uint8_t i = 0; i < _relayCount; ++i)
			{
				if (i != relayIndex && config->relay.relays[i].actionType == actionType)
					config->relay.relays[i].actionType = RelayActionType::Default;
			}
		}

		config->relay.relays[relayIndex].actionType = actionType;

		// Keep legacy index fields in sync by rescanning the relay array
		config->sound.hornRelayIndex = PinDisabled;
		config->lightSensor.nightRelayIndex = PinDisabled;
		for (uint8_t i = 0; i < _relayCount; ++i)
		{
			if (config->relay.relays[i].actionType == RelayActionType::Horn)
				config->sound.hornRelayIndex = i;
			else if (config->relay.relays[i].actionType == RelayActionType::NightRelay)
				config->lightSensor.nightRelayIndex = i;
		}

		if (_soundController != nullptr)
			_soundController->configUpdated(config);

		return RelayResult::Success;
	}

	RelayResult setRelayDefaultState(uint8_t relayIndex, bool defaultState)
	{
		Config* config = ConfigManager::getConfigPtr();
		if (config == nullptr)
			return RelayResult::InvalidConfig;

		if (relayIndex >= _relayCount)
			return RelayResult::InvalidIndex;

		config->relay.relays[relayIndex].defaultState = defaultState;
		return RelayResult::Success;
	}

	RelayResult linkRelays(uint8_t relay1, uint8_t relay2)
	{
		Config* config = ConfigManager::getConfigPtr();
		if (config == nullptr)
			return RelayResult::InvalidConfig;

		if (relay1 >= _relayCount || relay2 >= _relayCount)
			return RelayResult::InvalidIndex;

		for (uint8_t i = 0; i < ConfigMaxLinkedRelays; ++i)
		{
			if (config->relay.linkedRelays[i][0] == MaxUint8Value)
			{
				config->relay.linkedRelays[i][0] = relay1;
				config->relay.linkedRelays[i][1] = relay2;
				return RelayResult::Success;
			}
		}

		return RelayResult::Failed;
	}

	RelayResult unlinkRelay(uint8_t relay)
	{
		Config* config = ConfigManager::getConfigPtr();
		if (config == nullptr)
			return RelayResult::InvalidConfig;

		if (relay >= _relayCount)
			return RelayResult::InvalidIndex;

		for (uint8_t i = 0; i < ConfigMaxLinkedRelays; ++i)
		{
			if (config->relay.linkedRelays[i][0] == relay || config->relay.linkedRelays[i][1] == relay)
			{
				config->relay.linkedRelays[i][0] = MaxUint8Value;
				config->relay.linkedRelays[i][1] = MaxUint8Value;
			}
		}

		return RelayResult::Success;
	}

	RelayResult setRelayPin(uint8_t relayIndex, uint8_t pin)
	{
		Config* config = ConfigManager::getConfigPtr();
		if (config == nullptr)
			return RelayResult::InvalidConfig;

		if (relayIndex >= _relayCount)
			return RelayResult::InvalidIndex;

		if (pin == 0)
			return RelayResult::InvalidParameter;

		config->relay.relays[relayIndex].pin = pin;
		return RelayResult::Success;
	}

	RelayResult renameRelay(uint8_t relayIndex, const char* shortName, const char* longName)
	{
		Config* config = ConfigManager::getConfigPtr();
		if (config == nullptr)
			return RelayResult::InvalidConfig;

		if (relayIndex >= _relayCount)
			return RelayResult::InvalidIndex;

		strncpy(config->relay.relays[relayIndex].shortName, shortName, ConfigShortRelayNameLength - 1);
		config->relay.relays[relayIndex].shortName[ConfigShortRelayNameLength - 1] = '\0';
		strncpy(config->relay.relays[relayIndex].longName, longName, ConfigLongRelayNameLength - 1);
		config->relay.relays[relayIndex].longName[ConfigLongRelayNameLength - 1] = '\0';
		return RelayResult::Success;
	}

	RelayResult setButtonColor(uint8_t relayIndex, uint8_t color)
	{
		Config* config = ConfigManager::getConfigPtr();
		if (config == nullptr)
			return RelayResult::InvalidConfig;

		if (relayIndex >= _relayCount)
			return RelayResult::InvalidIndex;

		config->relay.relays[relayIndex].buttonImage = color;
		return RelayResult::Success;
	}
};
