k3ldar/PowerControlHub/PowerControlHub/LightSensorHandler.h

/*
 * PowerControlHub
 * Copyright (C) 2025 Simon Carter (s1cart3r@gmail.com)
 *
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
 * You should have received a copy of the GNU General Public License
 * along with this program. If not, see <https://www.gnu.org/licenses/>.
 */
#pragma once

#include "Local.h"
#include "BaseSensor.h"
#include "Queue.h"
#include "RelayController.h"

constexpr uint64_t LightCheckMs = 30000;
constexpr uint8_t LightQueueCapacity = 10;
constexpr uint8_t DaytimeConfirmReadings = 3;
constexpr uint8_t AnalogHysteresisPct = 10;

class LightSensorHandler : public BaseSensor, public BroadcastLoggerSupport
{
private:
    MessageBus* _messageBus;
    SensorCommandHandler* _sensorCommandHandler;
    RelayController* _relayController;
    const uint8_t _sensorPin;
    bool _isDigital;
    bool _isDaytime;
    bool _pendingDaytime;
    uint8_t _pendingDaytimeCount;
    Queue<uint16_t> _lightQueue;
    uint16_t _currentLightLevel;

#if defined(MQTT_SUPPORT)
    char _slugLight[28];
    char _slugLightLevel[32];
    char _slugAvgLightLevel[40];
    char _nameDaylight[48];
    char _nameLightLevel[48];
    char _nameAvgLightLevel[48];
#endif

    void syncNightRelay(Config* config)
    {
        if (config == nullptr || _relayController == nullptr)
            return;

        uint8_t nightRelay = DefaultValue;
        for (uint8_t i = 0; i < ConfigRelayCount; ++i)
        {
            if (config->relay.relays[i].actionType == RelayActionType::NightRelay)
            {
                nightRelay = i;
                break;
            }
        }

        if (nightRelay < ConfigRelayCount)
        {
            char buf[40];
            snprintf(buf, sizeof(buf), "relay=%u state=%s", nightRelay, !_isDaytime ? "on" : "off");
            sendDebug(buf, _name);
            _relayController->setRelayState(nightRelay, !_isDaytime);
        }
        else
        {
            char buf[40];
            snprintf(buf, sizeof(buf), "relay=%u skipped (disabled)", nightRelay);
            sendDebug(buf, _name);
        }
    }
    uint16_t effectiveAverage() const
    {
        return _isDigital ? _currentLightLevel : _lightQueue.average();
    }
protected:
    void initialize() override
    {
        pinMode(_sensorPin, INPUT);
        sendDebug(_isDigital ? "Mode: digital" : "Mode: analog", _name);
        syncNightRelay(ConfigManager::getConfigPtr());
    }

    uint64_t update() override
    {
        Config* config = ConfigManager::getConfigPtr();
        bool reading;

        if (_isDigital)
        {
            reading = digitalRead(_sensorPin) == LOW;
            _currentLightLevel = reading ? 1023 : 0;

            char buf[32];
            snprintf(buf, sizeof(buf), "pin=%d state=%s day=%d",
                _sensorPin, reading ? "HIGH" : "LOW", _isDaytime ? 1 : 0);
            sendDebug(buf, _name);
        }
        else
        {
            _currentLightLevel = static_cast<uint16_t>(analogRead(_sensorPin));
            _lightQueue.enqueue(_currentLightLevel);

            uint16_t avgLevel = _lightQueue.average();
            uint16_t threshold = (config != nullptr) ? config->lightSensor.daytimeThreshold : 512;
            uint16_t hysteresis = static_cast<uint16_t>((static_cast<uint32_t>(threshold) * AnalogHysteresisPct) / 100U);

            if (hysteresis == 0)
                hysteresis = 1;
            
            uint16_t lower = (threshold > hysteresis) ? threshold - hysteresis : 0;
            uint16_t upper = (threshold + hysteresis > 1023) ? 1023 : threshold + hysteresis;
            reading = _isDaytime ? (avgLevel > lower) : (avgLevel > upper);

            char buf[64];
            snprintf(buf, sizeof(buf), "level=%u avg=%u lo=%u hi=%u day=%d",
                _currentLightLevel, avgLevel, lower, upper, _isDaytime ? 1 : 0);
            sendDebug(buf, _name);
        }

        if (reading == _pendingDaytime)
        {
            if (_pendingDaytimeCount < DaytimeConfirmReadings)
                _pendingDaytimeCount++;
        }
        else
        {
            char buf[40];
            snprintf(buf, sizeof(buf), "Pending flip: %s count reset", reading ? "day" : "night");
            sendDebug(buf, _name);
            _pendingDaytime = reading;
            _pendingDaytimeCount = 1;
        }

        if (_pendingDaytimeCount >= DaytimeConfirmReadings && _isDaytime != _pendingDaytime)
        {
            _isDaytime = _pendingDaytime;

            char buf[24];
            snprintf(buf, sizeof(buf), "State -> %s", _isDaytime ? "day" : "night");
            sendDebug(buf, _name);
            syncNightRelay(config);
        }

        if (_messageBus)
        {
            _messageBus->publish<LightSensorUpdated>(_isDaytime, _currentLightLevel, effectiveAverage());
        }

        StringKeyValue params;
        strncpy(params.key, ValueParamName, sizeof(params.key));
        snprintf(params.value, sizeof(params.value), "%d", _isDaytime);
        sendCommand(SensorLightSensor, &params, 1);

        if (_sensorCommandHandler)
        {
            _sensorCommandHandler->setDaytime(_isDaytime);
        }

        return LightCheckMs;
    }

public:
    LightSensorHandler(MessageBus* messageBus, BroadcastManager* broadcastManager, SensorCommandHandler* sensorCommandHandler,
        RelayController* relayController, uint8_t sensorPin, bool isDigital, const char* name = "LightSensor")
        : BaseSensor(name), BroadcastLoggerSupport(broadcastManager),
          _messageBus(messageBus), _sensorCommandHandler(sensorCommandHandler),
          _relayController(relayController), _sensorPin(sensorPin), _isDigital(isDigital),
          _isDaytime(true), _pendingDaytime(true), _pendingDaytimeCount(DaytimeConfirmReadings),
          _lightQueue(LightQueueCapacity), _currentLightLevel(0)
    {
#if defined(MQTT_SUPPORT)
        snprintf(_slugLight, sizeof(_slugLight), "%s_light", _safeSlug);
        snprintf(_slugLightLevel, sizeof(_slugLightLevel), "%s_light_level", _safeSlug);
        snprintf(_slugAvgLightLevel, sizeof(_slugAvgLightLevel), "%s_avg_light_level", _safeSlug);
        snprintf(_nameDaylight, sizeof(_nameDaylight), "%s Daylight", _name);
        snprintf(_nameLightLevel, sizeof(_nameLightLevel), "%s Light Level", _name);
        snprintf(_nameAvgLightLevel, sizeof(_nameAvgLightLevel), "%s Avg Light Level", _name);
#endif
    }

    void formatStatusJson(char* buffer, size_t size) override
    {
        snprintf(buffer, size, "\"isDaytime\":%s,\"lightLevel\":%u,\"avgLightLevel\":%u",
            _isDaytime ? "true" : "false",
            _currentLightLevel,
            effectiveAverage());
    }

    SensorIdList getSensorIdType() const override
    {
        return SensorIdList::LightSensor;
    }

    SensorType getSensorType() const override
    {
        return SensorType::Local;
    }

    const char* getSensorCommandId() const override
    {
        return SensorLightSensor;
    }

    uint16_t getLightLevel() const
    {
        return _currentLightLevel;
    }

    uint16_t getAverageLightLevel() const
    {
        return effectiveAverage();
    }

#if defined(MQTT_SUPPORT)

    uint8_t getMqttChannelCount() const override
    {
        return 3;
    }

    MqttSensorChannel getMqttChannel(uint8_t channelIndex) const override
    {
        switch (channelIndex)
        {
            case 1: return { _nameLightLevel, _slugLightLevel, "light_level", nullptr, nullptr, false };
            case 2: return { _nameAvgLightLevel, _slugAvgLightLevel, "avg_light_level", nullptr, nullptr, false };
            default: return { _nameDaylight, _slugLight, "light", "light", nullptr, true  };
        }
    }

    void getMqttValue(uint8_t channelIndex, char* buffer, size_t size) const override
    {
        if (!buffer || size == 0)
            return;

        switch (channelIndex)
        {
            case 1: snprintf(buffer, size, "%u", _currentLightLevel); break;
            case 2: snprintf(buffer, size, "%u", effectiveAverage()); break;
            default: snprintf(buffer, size, "%s", _isDaytime ? "ON" : "OFF"); break;
        }
    }
#endif
};
