k3ldar/PowerControlHub/PowerControlHub/ScheduleController.h

/*
 * PowerControlHub
 * Copyright (C) 2025 Simon Carter (s1cart3r@gmail.com)
 *
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
 * You should have received a copy of the GNU General Public License
 * along with this program. If not, see <https://www.gnu.org/licenses/>.
 */
#pragma once

#include "Config.h"

#include "RelayController.h"
#include "MessageBus.h"
#include "ConfigManager.h"

constexpr int16_t SunTimeUnknown = -1;
constexpr uint64_t ScheduleCheckIntervalMs = 1000UL;

constexpr uint16_t MinutesPerDay = 1440u;
constexpr uint64_t MsPerMinute = 60000UL;
constexpr uint64_t MsPerSecond = 1000UL;
constexpr uint16_t NeverFiredMinute = 0xFFFFu;

class ScheduleController
{
private:
    RelayController* _relayController;
    MessageBus*      _messageBus;

    // Per-event runtime state (not persisted — reset on boot)
    uint32_t      _lastFiredDay[ConfigMaxScheduledEvents];       // packed YYYYMMDD of last fire
    uint16_t      _lastFiredMinute[ConfigMaxScheduledEvents];    // minute-of-day (0-1439) of last fire
    uint64_t _lastIntervalFireMs[ConfigMaxScheduledEvents]; // SystemFunctions::millis64() of last interval fire
    uint64_t _pulseStartMs[ConfigMaxScheduledEvents];       // SystemFunctions::millis64() when pulse started
    uint64_t _pulseDurMs[ConfigMaxScheduledEvents];         // pulse duration in ms
    uint8_t       _pulseRelayIdx[ConfigMaxScheduledEvents];      // relay index for active pulse
    bool          _pulseActive[ConfigMaxScheduledEvents];        // true while pulse relay is on

    // Light / position state (updated via MessageBus)
    bool    _isDayTime;
    double  _gpsLat;
    double  _gpsLon;
    bool    _hasGps;
    int16_t _sunriseMinutes; // local minutes from midnight, SunTimeUnknown if unavailable
    int16_t _sunsetMinutes;  // local minutes from midnight, SunTimeUnknown if unavailable
    uint32_t _sunCalcDay;    // packed YYYYMMDD for which sun times were computed

    uint64_t _lastCheckMs;

    // Returns true when the trigger for event idx is due to fire right now
    bool isTriggerDue(uint8_t idx,
        const ScheduledEvent& ev,
        uint8_t hour, uint8_t minute,
        uint8_t dowBit,
        uint8_t day, uint8_t month,
        uint32_t today,
        uint64_t now);

    // Returns true when all conditions for the event are satisfied
    bool isConditionMet(const ScheduledEvent& ev,
                        uint8_t hour, uint8_t minute,
                        uint8_t dowBit) const;

    // Executes the action associated with an event
    void executeAction(uint8_t idx, const ScheduledEvent& ev, uint64_t now);

    // Turns off any relay pulses whose duration has expired
    void updatePulses(uint64_t now);

    // Recomputes sunrise/sunset minute-of-day values for the given date
    void recomputeSunTimes(uint16_t year, uint8_t month, uint8_t day);

    // NOAA simplified solar calculation; returns local minutes from midnight
    static void calcSunTimes(double lat, double lon,
                             uint16_t year, uint8_t month, uint8_t day,
                             int16_t& sunriseMin, int16_t& sunsetMin);

    // Returns the day-of-week bitmask bit for a date (bit0=Mon .. bit6=Sun)
    static uint8_t calcDayOfWeekBit(uint16_t year, uint8_t month, uint8_t day);

    // Packs year/month/day into a uint32 YYYYMMDD key
    static uint32_t encodeDay(uint16_t year, uint8_t month, uint8_t day);

public:
    ScheduleController(RelayController* relayController, MessageBus* messageBus);

    // Subscribe to MessageBus events — call once during setup
    void begin();

    void update(uint64_t now);
};
