k3ldar/PowerControlHub/PowerControlHub/MQTTSensorHandler.h

/*
 * PowerControlHub
 * Copyright (C) 2025 Simon Carter (s1cart3r@gmail.com)
 *
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
 * You should have received a copy of the GNU General Public License
 * along with this program. If not, see <https://www.gnu.org/licenses/>.
 */
#pragma once

#include "MQTTHandler.h"
#include "ConfigManager.h"
#include "SensorController.h"
#include "SystemFunctions.h"
#include <vector>
#include <map>

// Forward declaration
class SerialCommandManager;

struct MqttChannelMap
{
    BaseSensor* sensor;
    uint8_t channelIndex;
    const char* typeSlug;
    uint64_t lastPublishTime;
    uint64_t publishIntervalMs;
};

class MQTTSensorHandler : public MQTTHandler
{
private:
    Config* _config;
    SensorController* _sensorController;
    SerialCommandManager* _commandMgr;

    // Channel map (built during begin())
    std::vector<MqttChannelMap> _channelMap;

    // Map from typeSlug to channel indices for fast event handler lookup (Option 1)
    // Using std::map with custom string comparator for embedded compatibility
    struct StrCompare {
        bool operator()(const char* a, const char* b) const {
            if (a == nullptr && b == nullptr) return false;
            if (a == nullptr) return true;
            if (b == nullptr) return false;
            return strcmp(a, b) < 0;
        }
    };
    std::map<const char*, std::vector<uint8_t>, StrCompare> _typeSlugToIndices;

    // Discovery state
    bool _discoveryPending;
    uint8_t _discoveryIndex;
    uint64_t _lastDiscoveryPublish;

    static constexpr uint16_t MinPublishInterval = 200;

    void publishSensorState(uint8_t channelIndex);
    void publishDiscoveryConfig();
    void publishSensorDiscoveryConfig(uint8_t index);
    void onTemperatureUpdated(float temperature);
    void onHumidityUpdated(uint8_t humidity);
    void onLightSensorUpdated(bool isDaytime, uint16_t lightLevel, uint16_t averageLightLevel);
    void onWaterLevelUpdated(uint16_t waterLevel, uint16_t averageWaterLevel);

public:
    MQTTSensorHandler(MQTTController* mqttController, MessageBus* messageBus, SensorController* sensorController, SerialCommandManager* commandMgr = nullptr);

    bool begin() override;
    void update() override;
    void end() override;

    void onMessage(const char* topic, const char* payload) override;

    bool subscribe() override;
    void unsubscribe() override;
};
