k3ldar/PowerControlHub/PowerControlHub/SensorCommandHandler.h

/*
 * PowerControlHub
 * Copyright (C) 2025 Simon Carter (s1cart3r@gmail.com)
 *
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
 * You should have received a copy of the GNU General Public License
 * along with this program. If not, see <https://www.gnu.org/licenses/>.
 */
#pragma once

#include <Arduino.h>
#include "SerialCommandManager.h"
#include "Local.h"
#include "BaseNextionCommandHandler.h"

class RemoteSensor;

class SensorCommandHandler : public BaseNextionCommandHandler
{
private:
	float _lastTemperature = NAN;
	uint8_t _lastHumidity = 0;
	float _lastBearing = NAN;
	float _lastCompassTemp = 0;
	uint8_t _lastSpeed = 0;
	uint16_t _lastWaterLevel = 0;
	bool _lastWaterPumpActive = false;
	bool _isDaytime = true;
	double _gpsLatitude;
	double _gpsLongitude;
	double _altitude;
	double _gpsCourse;
	uint32_t _gpsSatellites;
	const char* _gpsDirection;
	double _gpsDistance = 0;
    bool _lastHornActive = false;
	RemoteSensor** _remoteSensors;
	size_t _remoteSensorCount;

public:
	explicit SensorCommandHandler(BroadcastManager* broadcastManager, 
		MessageBus* messageBus,
		WarningManager* warningManager);

    bool handleCommand(SerialCommandManager* sender, const char* command, const StringKeyValue params[], uint8_t paramCount) override;
    const char* const* supportedCommands(size_t& count) const override;

	void setup(RemoteSensor* remoteSensors[], size_t remoteSensorCount);


	// Getters
	float getTemperature() const;
	uint8_t getHumidity() const;
	float getBearing() const;
	float getCompassTemperature() const;
	uint8_t getSpeed() const;
	uint16_t getWaterLevel() const;
	bool getWaterPumpActive() const;
	bool getIsDaytime() const;
	double getGpsLatitude() const;
	double getGpsLongitude() const;
	double getGpsAltitude() const;
	double getGpsCourse() const;
	double getGpsDistance() const;
	const char* getGpsDirection() const;
	uint32_t getGpsSatellites() const;
	bool getHornActive() const;
	

	// Setters
	void setTemperature(float value);
	void setHumidity(uint8_t value);
	void setBearing(float value);
	void setCompassTemperature(float value);
	void setSpeed(uint8_t value);
	void setWaterLevel(uint16_t value);
	void setWaterPumpActive(bool value);
	void setDaytime(bool isDaytime);
	void setGpsLocation(double lat, double lon);
	void setGpsAltitude(double alt);
	void setGpsCourse(double course);
	void setGpsSatellites(uint32_t sats);
	void setGpsDirection(const char* dir);
	void setGpsDistance(double distance);
	void setHornActive(bool value);
};
