k3ldar/PowerControlHub/PowerControlHub/PageRelaySettings.cpp

/*
 * PowerControlHub
 * Copyright (C) 2025 Simon Carter (s1cart3r@gmail.com)
 *
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
 * You should have received a copy of the GNU General Public License
 * along with this program. If not, see <https://www.gnu.org/licenses/>.
 */

#include "PageRelaySettings.h"

#if defined(NEXTION_DISPLAY_DEVICE)
#include "SystemFunctions.h"

static const char SettingsError[] PROGMEM = "tRelayError";
static const char SettingSelectedText[] PROGMEM = "tSelected";
static const char PropertyButtonColor[] PROGMEM = "bco";
static const char SettingRelayButton1[] PROGMEM = "b0";
static const char SettingRelayButton2[] PROGMEM = "b1";
static const char SettingRelayButton3[] PROGMEM = "b2";
static const char SettingRelayButton4[] PROGMEM = "b4";
static const char SettingRelayButton5[] PROGMEM = "b5";
static const char SettingRelayButton6[] PROGMEM = "b6";
static const char SettingRelayButton7[] PROGMEM = "b7";
static const char SettingRelayButton8[] PROGMEM = "b8";
static const char* const  SettingRelayButtons[] PROGMEM = {
    SettingRelayButton1, SettingRelayButton2, SettingRelayButton3,
    SettingRelayButton4, SettingRelayButton5, SettingRelayButton6,
    SettingRelayButton7, SettingRelayButton8
};

// global variable of page that is currently being configured
static const char SettingsRelaySetupId[] PROGMEM = "relaySetupId";
// global variable for maximum number of relays to select
static const char SettingsMaxSelectionCount[] PROGMEM = "relayMaximumSelectionCount";


// Nextion Names/Ids on current Page
constexpr uint8_t ButtonPrevious = 3;
constexpr uint8_t ButtonNext = 2;

constexpr uint16_t ButtonSelected = 5990;
constexpr uint16_t ButtonNotSelected = 65535;

// home page button selection
constexpr uint8_t relayHomePageSetupId = 0;

// always on button selection
constexpr uint8_t relayDefaultOn = 1;

// allows user to have a dedicated horn relay
constexpr uint8_t relayHornRelay = 2;

// associate button selection, two relays can be associated together so 
// on together and off together, you can have two of these associations
constexpr uint8_t relayAssociate1 = 3;
constexpr uint8_t relayAssociate2 = 4;

//page allowing users to select custom colors for each relay button that is on
constexpr uint8_t relayColorSelection = 5;

// page allowing user to select night relay 
constexpr uint8_t relayNightRelay = 6;

PageRelaySettings::PageRelaySettings(Stream* serialPort,
    WarningManager* warningMgr,
    SerialCommandManager* commandMgrComputer)
    : BasePage(serialPort, warningMgr, commandMgrComputer),
    _currentSettingsIndex(relayHomePageSetupId)
{
    _externalData[0] = '\0';
}

void PageRelaySettings::onEnterPage()
{
	Config* config = getConfig();

    if (!config)
        return;

	for (uint8_t i = 0; i < ConfigRelayCount; i++)
    {
        const char* buttonName = reinterpret_cast<const char*>(pgm_read_ptr(&SettingRelayButtons[i]));
        sendText(reinterpret_cast<const __FlashStringHelper*>(buttonName), config->relay.relays[i].shortName);
    }

    _currentSettingsIndex = relayHomePageSetupId;
    loadConfigPage();
}

void PageRelaySettings::begin()
{
    // not used just now
}

void PageRelaySettings::refresh(unsigned long now)
{
    (void)now;
    //nothing to refresh currently
}

// Handle touch events for buttons
void PageRelaySettings::handleTouch(uint8_t compId, uint8_t eventType)
{
    (void)eventType;

    switch (compId)
    {
    case ButtonPrevious:
        if (_currentSettingsIndex > relayHomePageSetupId)
        {
            _currentSettingsIndex--;
        }
        break;
    case ButtonNext:
        if (validateExternalData())
        {
            _currentSettingsIndex++;
        }
        break;

    default:
        // Unknown component
        return;
    }

    loadConfigPage();
}

void PageRelaySettings::loadConfigPage()
{
    Config* config = getConfig();

    if (!config)
        return;

	clearSelection();

    switch (_currentSettingsIndex)
    {
        case relayHomePageSetupId:
        {
            sendValue(FPSTR(SettingsRelaySetupId), relayHomePageSetupId);

            // Load the 4 selected relay indices and set their button colors
            for (uint8_t i = 0; i < ConfigHomeButtons; i++)
            {
                uint8_t relayIndex = config->relay.homePageMapping[i];
                
                if (relayIndex < ConfigRelayCount)
                {
                    const char* buttonName = reinterpret_cast<const char*>(pgm_read_ptr(&SettingRelayButtons[relayIndex]));
                    setComponentProperty(reinterpret_cast<const __FlashStringHelper*>(buttonName),
                        FPSTR(PropertyButtonColor), ButtonSelected);
                }
                
                _externalData[i] = '0' + relayIndex;
            }

            _externalData[ConfigHomeButtons] = '\0';
            sendText(FPSTR(SettingSelectedText), _externalData);

            break;
        }

        case relayDefaultOn:
        {
            sendValue(FPSTR(SettingsRelaySetupId), relayDefaultOn);
            uint8_t selectionCount = 0;

            for (uint8_t i = 0; i < ConfigRelayCount; i++)
            {
                bool selButton = config->relay.relays[i].defaultState;
                uint16_t buttonColor = selButton ? ButtonSelected : ButtonNotSelected;
                const char* buttonName = reinterpret_cast<const char*>(pgm_read_ptr(&SettingRelayButtons[i]));

                setComponentProperty(reinterpret_cast<const __FlashStringHelper*>(buttonName),
                    FPSTR(PropertyButtonColor), buttonColor);

                if (selButton)
                {
                    _externalData[selectionCount] = '0' + i;
                    selectionCount++;
                }
            }

            _externalData[selectionCount] = '\0';
            sendText(FPSTR(SettingSelectedText), _externalData);

            break;
        }

        case relayHornRelay:
        {
            sendValue(FPSTR(SettingsRelaySetupId), relayHornRelay);

            uint8_t hornIndex = config->sound.hornRelayIndex;
            
            for (uint8_t i = 0; i < ConfigRelayCount; i++)
            {
                uint16_t buttonColor = (hornIndex == i) ? ButtonSelected : ButtonNotSelected;
                const char* buttonName = reinterpret_cast<const char*>(pgm_read_ptr(&SettingRelayButtons[i]));
                setComponentProperty(reinterpret_cast<const __FlashStringHelper*>(buttonName),
                    FPSTR(PropertyButtonColor), buttonColor);
            }

            // Populate _externalData with current selection
            if (hornIndex < ConfigRelayCount)
            {
                _externalData[0] = '0' + hornIndex;
                _externalData[1] = '\0';
            }
            else
            {
                _externalData[0] = '\0';
            }
            
            sendText(FPSTR(SettingSelectedText), _externalData);

            break;
        }

        case relayAssociate1:
        {
            sendValue(FPSTR(SettingsRelaySetupId), relayAssociate1);

            uint8_t selectionCount = 0;

            // Iterate through all 8 relay buttons
            for (uint8_t i = 0; i < ConfigRelayCount; i++)
            {
                bool isSelected = false;
                
                // Check if this relay is in the linked pair
                for (uint8_t j = 0; j < ConfigLinkedRelayCount; j++)
                {
                    if (config->relay.linkedRelays[0][j] == i && config->relay.linkedRelays[0][j] < ConfigRelayCount)
                    {
                        isSelected = true;
                        _externalData[selectionCount] = '0' + i;
                        selectionCount++;
                        break;
                    }
                }

                uint16_t buttonColor = isSelected ? ButtonSelected : ButtonNotSelected;
                const char* buttonName = reinterpret_cast<const char*>(pgm_read_ptr(&SettingRelayButtons[i]));
                setComponentProperty(reinterpret_cast<const __FlashStringHelper*>(buttonName),
                    FPSTR(PropertyButtonColor), buttonColor);
            }

            _externalData[selectionCount] = '\0';
            sendText(FPSTR(SettingSelectedText), _externalData);

            break;
        }

        case relayAssociate2:
        {
            sendValue(FPSTR(SettingsRelaySetupId), relayAssociate2);

            uint8_t selectionCount = 0;

            // Iterate through all 8 relay buttons
            for (uint8_t i = 0; i < ConfigRelayCount; i++)
            {
                bool isSelected = false;
                
                // Check if this relay is in the linked pair
                for (uint8_t j = 0; j < ConfigLinkedRelayCount; j++)
                {
                    if (config->relay.linkedRelays[1][j] == i && config->relay.linkedRelays[1][j] < ConfigRelayCount)
                    {
                        isSelected = true;
                        _externalData[selectionCount] = '0' + i;
                        selectionCount++;
                        break;
                    }
                }

                uint16_t buttonColor = isSelected ? ButtonSelected : ButtonNotSelected;
                const char* buttonName = reinterpret_cast<const char*>(pgm_read_ptr(&SettingRelayButtons[i]));
                setComponentProperty(reinterpret_cast<const __FlashStringHelper*>(buttonName),
                    FPSTR(PropertyButtonColor), buttonColor);
            }

            _externalData[selectionCount] = '\0';
            sendText(FPSTR(SettingSelectedText), _externalData);

            break;
        }

        case relayColorSelection:
        {
            sendValue(FPSTR(SettingsRelaySetupId), relayColorSelection);

            // Load current button image selections and set button colors
            for (uint8_t i = 0; i < ConfigRelayCount; i++)
            {
                uint8_t imageId = config->relay.relays[i].buttonImage;
                
                // Map image ID to character (1-5, default to white)
                char colorChar;
                uint16_t buttonColor;
                
                switch (imageId)
                {
                    case ImageButtonColorBlue:
                        colorChar = '1';
                        buttonColor = 1055;
                        break;
                    case ImageButtonColorGreen:
                        colorChar = '2';
                        buttonColor = 2024;
                        break;
                    case ImageButtonColorOrange:
                        colorChar = '3';
                        buttonColor = 64520;
                        break;
                    case ImageButtonColorRed:
                        colorChar = '4';
                        buttonColor = 63488;
                        break;
                    case ImageButtonColorYellow:
                        colorChar = '5';
                        buttonColor = 65504;
                        break;
                    default:
                        colorChar = '0';
                        buttonColor = 65535;
                        break;
                }
                
                _externalData[i] = colorChar;
                
                const char* buttonName = reinterpret_cast<const char*>(pgm_read_ptr(&SettingRelayButtons[i]));
                setComponentProperty(reinterpret_cast<const __FlashStringHelper*>(buttonName),
                    FPSTR(PropertyButtonColor), buttonColor);
            }

            _externalData[ConfigRelayCount] = '\0';
            sendText(FPSTR(SettingSelectedText), _externalData);

            break;
        }
        case relayNightRelay:
        {
            sendValue(FPSTR(SettingsRelaySetupId), relayNightRelay);

            uint8_t nightRelayIdx = config->lightSensor.nightRelayIndex;

            for (uint8_t i = 0; i < ConfigRelayCount; i++)
            {
                uint16_t buttonColor = (nightRelayIdx == i) ? ButtonSelected : ButtonNotSelected;
                const char* buttonName = reinterpret_cast<const char*>(pgm_read_ptr(&SettingRelayButtons[i]));
                setComponentProperty(reinterpret_cast<const __FlashStringHelper*>(buttonName),
                    FPSTR(PropertyButtonColor), buttonColor);
            }

            if (nightRelayIdx < ConfigRelayCount)
            {
                _externalData[0] = '0' + nightRelayIdx;
                _externalData[1] = '\0';
            }
            else
            {
                _externalData[0] = '\0';
            }

            sendText(FPSTR(SettingSelectedText), _externalData);

            break;
        }
        default:
            ConfigManager::save();
            navigateTo(PageIdAbout);
    }
}

void PageRelaySettings::handleText(const char* text)
{
    if (text == nullptr)
    {
        _externalData[0] = '\0';
        return;
    }

    if (strlen(text) >= sizeof(_externalData))
    {
        strncpy(_externalData, text, sizeof(_externalData) - 1);
        _externalData[sizeof(_externalData) - 1] = '\0';
    }
    else
    {
        snprintf_P(_externalData, sizeof(_externalData), PSTR("%s"), text);
    }
}
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
