k3ldar/PowerControlHub/PowerControlHub/PageSettings.cpp

/*
 * PowerControlHub
 * Copyright (C) 2025 Simon Carter (s1cart3r@gmail.com)
 *
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
 * You should have received a copy of the GNU General Public License
 * along with this program. If not, see <https://www.gnu.org/licenses/>.
 */

#include "PageSettings.h"

#if defined(NEXTION_DISPLAY_DEVICE)
#include "ConfigManager.h"
#include "SystemFunctions.h"

static const char SettingsKeyboardInputLen[] PROGMEM = "keyboardInputLen";
static const char SettingsKeyboardNumericOnly[] PROGMEM = "keyboardNumericOnly";
static const char SettingsName[] PROGMEM = "tName";
static const char SettingsError[] PROGMEM = "tError";
static const char SettingsValue[] PROGMEM = "tValue";
static const char SettingsNextButton[] PROGMEM = "b32";
static const char SettingsNext[] PROGMEM = "Next";
static const char SettingsSave[] PROGMEM = "Save";

static const char SettingsBoatName[] PROGMEM = "Boat Name";
static const char SettingsCallSign[] PROGMEM = "Call Sign";
static const char SettingsMmsiNumber[] PROGMEM = "MMSI Number";
static const char SettingsHomePort[] PROGMEM = "Home Port";
static const char ShortRelayDescription[] PROGMEM = "Short Relay Name %d";
static const char LongRelayDescription[] PROGMEM = "Long Relay Name %d";


// Nextion Names/Ids on current Page
constexpr uint8_t ButtonPrevious = 4;
constexpr uint8_t ButtonNext = 29;

constexpr uint8_t ShowNumericKeyboard = 0;
constexpr uint8_t ShowAlphaKeyboard = 1;

constexpr uint8_t SettingBoatName = 0;
constexpr uint8_t SettingBoatNameLen = 30;

constexpr uint8_t SettingCallSign = 1;
constexpr uint8_t SettingCallSignLen = 10;

constexpr uint8_t SettingMmsiNumber = 2;
constexpr uint8_t SettingMmsiNumberLen = 9;

constexpr uint8_t SettingHomePortName = 3;

constexpr uint8_t SettingShortRelayOffset = 4;
constexpr uint8_t SettingShortRelay1 = 4;
constexpr uint8_t SettingShortRelay2 = 5;
constexpr uint8_t SettingShortRelay3 = 6;
constexpr uint8_t SettingShortRelay4 = 7;
constexpr uint8_t SettingShortRelay5 = 8;
constexpr uint8_t SettingShortRelay6 = 9;
constexpr uint8_t SettingShortRelay7 = 10;
constexpr uint8_t SettingShortRelay8 = 11;

constexpr uint8_t SettingLongRelayOffset = 12;
constexpr uint8_t SettingLongRelay1 = 12;
constexpr uint8_t SettingLongRelay2 = 13;
constexpr uint8_t SettingLongRelay3 = 14;
constexpr uint8_t SettingLongRelay4 = 15;
constexpr uint8_t SettingLongRelay5 = 16;
constexpr uint8_t SettingLongRelay6 = 17;
constexpr uint8_t SettingLongRelay7 = 18;
constexpr uint8_t SettingLongRelay8 = 19;


constexpr uint8_t LastSettings = 19;

PageSettings::PageSettings(Stream* serialPort,
    WarningManager* warningMgr,
    SerialCommandManager* commandMgrComputer)
    : BasePage(serialPort, warningMgr,  commandMgrComputer),
    _currentSettingsIndex(SettingBoatName)
{
	_externalData[0] = '\0';
}

void PageSettings::onEnterPage()
{
    _currentSettingsIndex = SettingBoatName;
    loadConfigPage();
}

void PageSettings::begin()
{
    // not used just now
}

void PageSettings::refresh(unsigned long now)
{
	(void)now;
    //nothing to refresh currently
}
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
